oleroma/Grip/media/dev/2.jpg

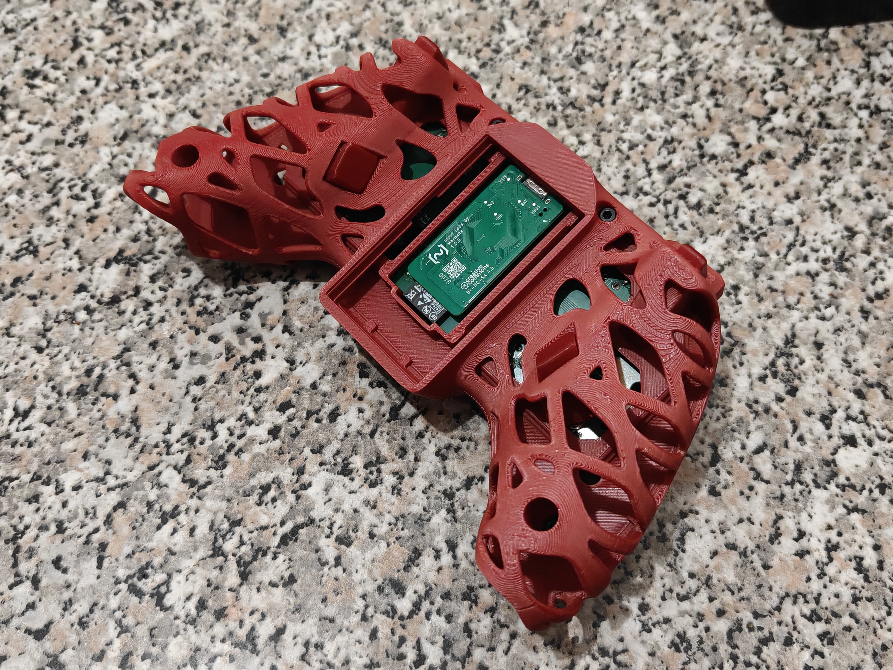
media/dev/2.jpg
