oleroma/Grip/media/dev/3.jpg

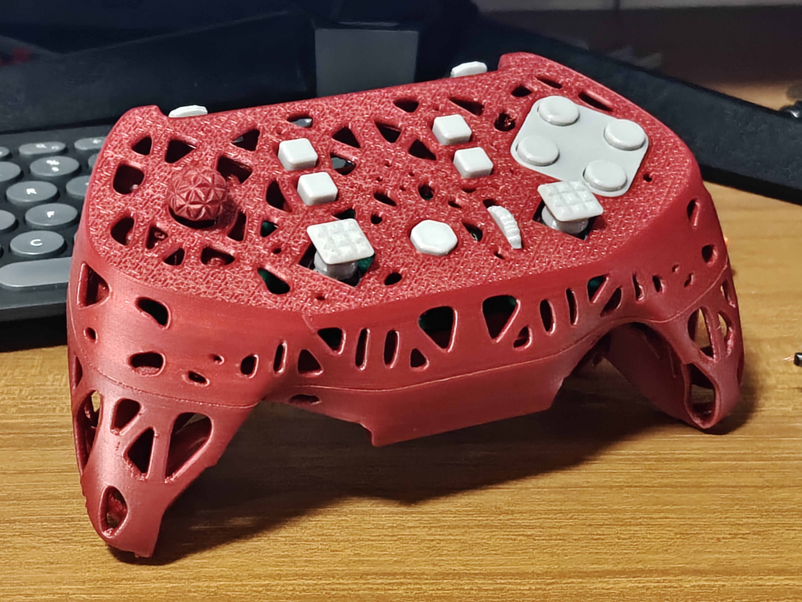
media/dev/3.jpg
