oleroma/Grip/media/dev/4.jpg

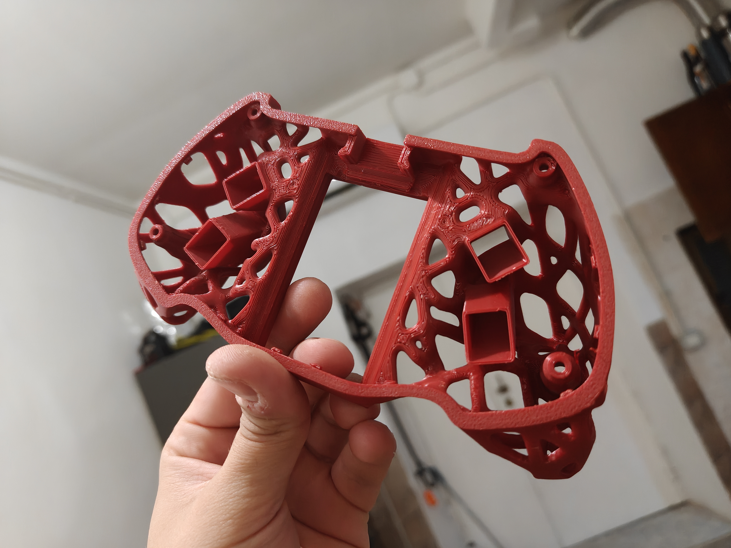
media/dev/4.jpg
