oleroma/Grip/media/dev/GripV_detail.jpg

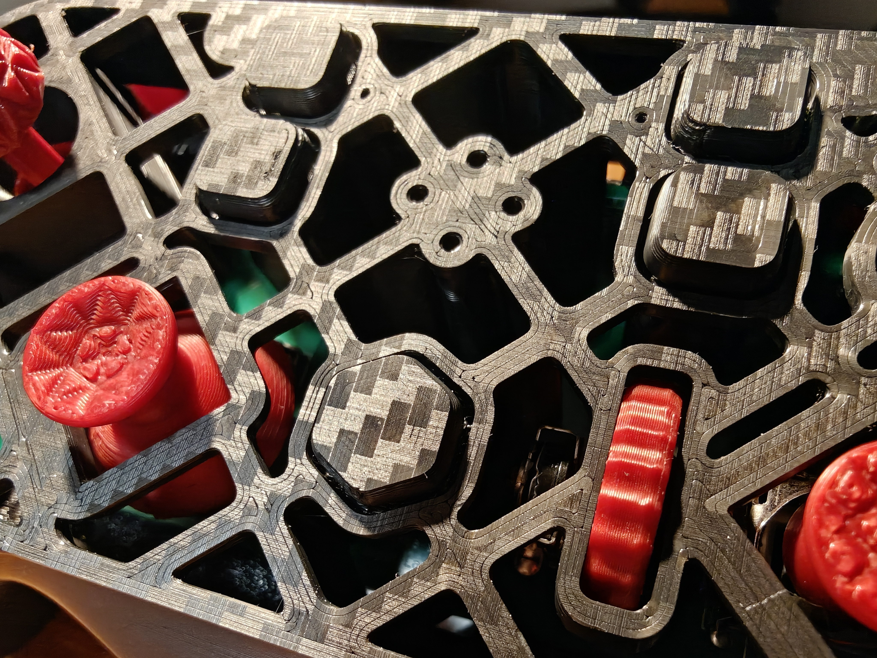
media/dev/GripV_detail.jpg
