oleroma/Grip/media/previews/1.png

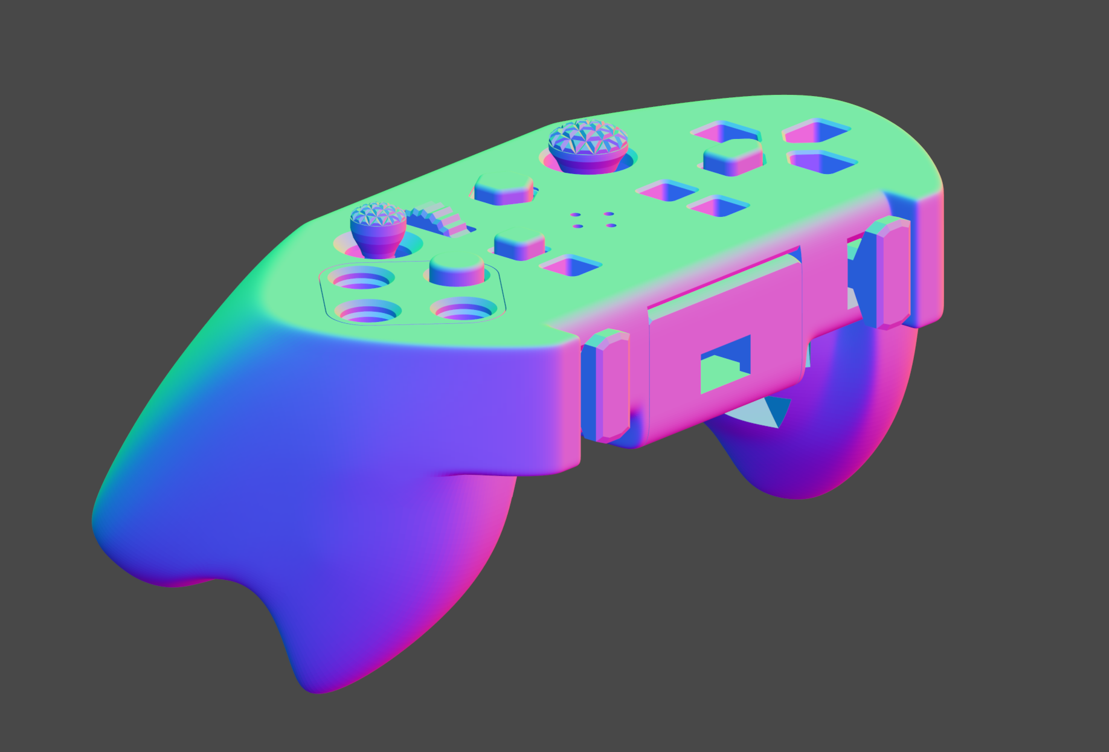
media/previews/1.png
