oleroma/Grip/media/previews/2.png

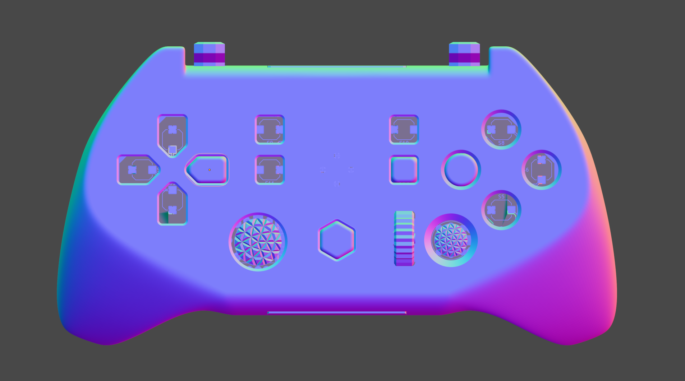
media/previews/2.png
