oleroma/Grip/media/previews/3.png

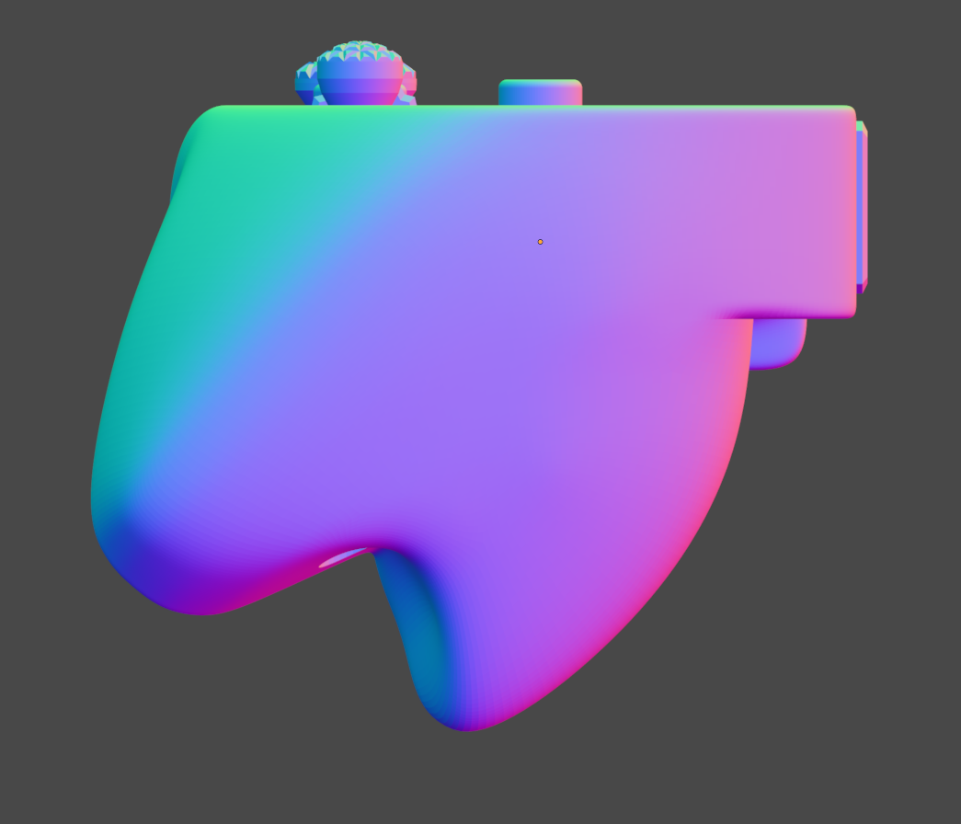
media/previews/3.png
