oleroma/Grip/media/previews/4.png

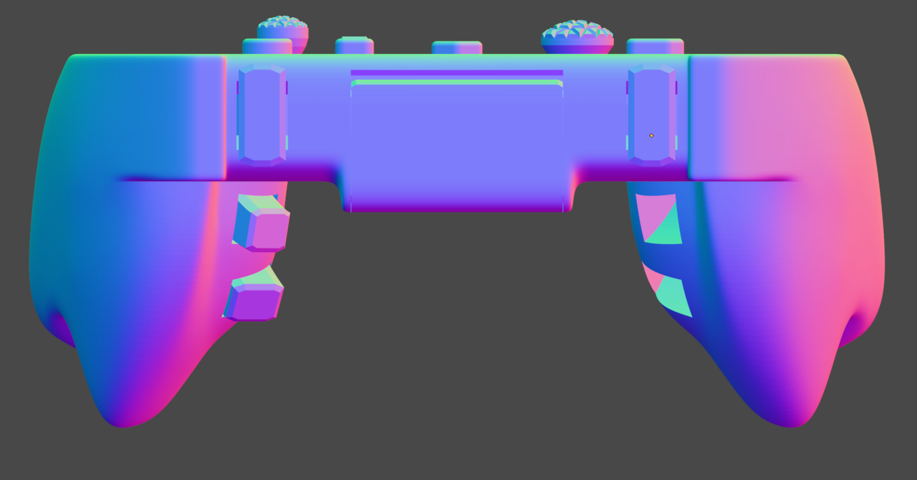
media/previews/4.png
