oleroma/Grip/media/previews/5.png

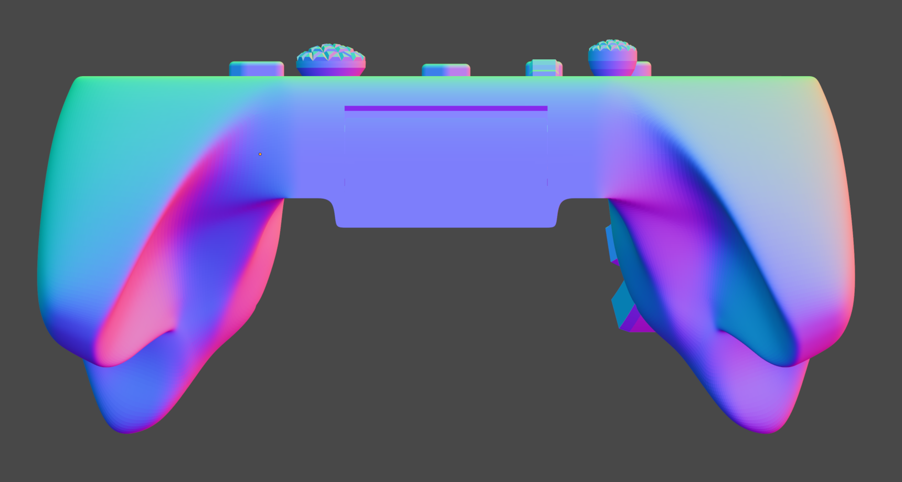
media/previews/5.png
