oleroma/Grip/media/previews/6.png

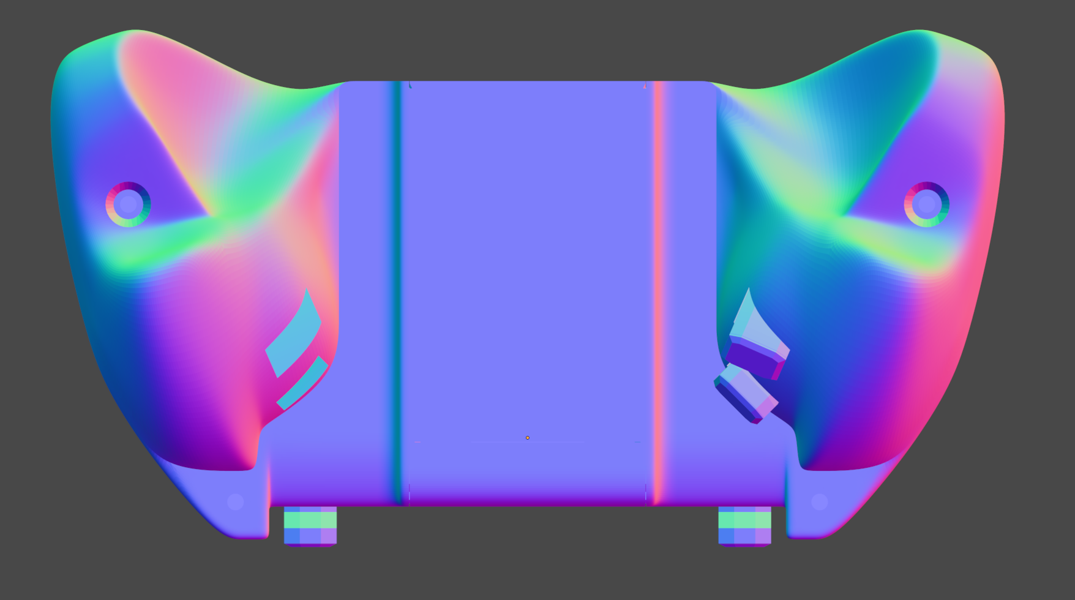
media/previews/6.png
