oleroma/Grip/orca_slicer/GripV/parts/buttons/loose/select_button.stl

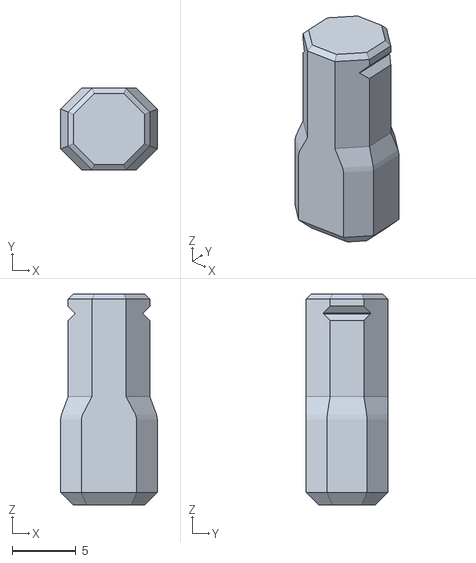
[picture p30: CAD file, 2026-09-15]
orca_slicer/GripV/parts/buttons/loose/select_button.stl
7.60 x 6.40 x 16.6
