oleroma/Grip/orca_slicer/GripV/parts/dpad_stick/dpad_stick_cap.stl

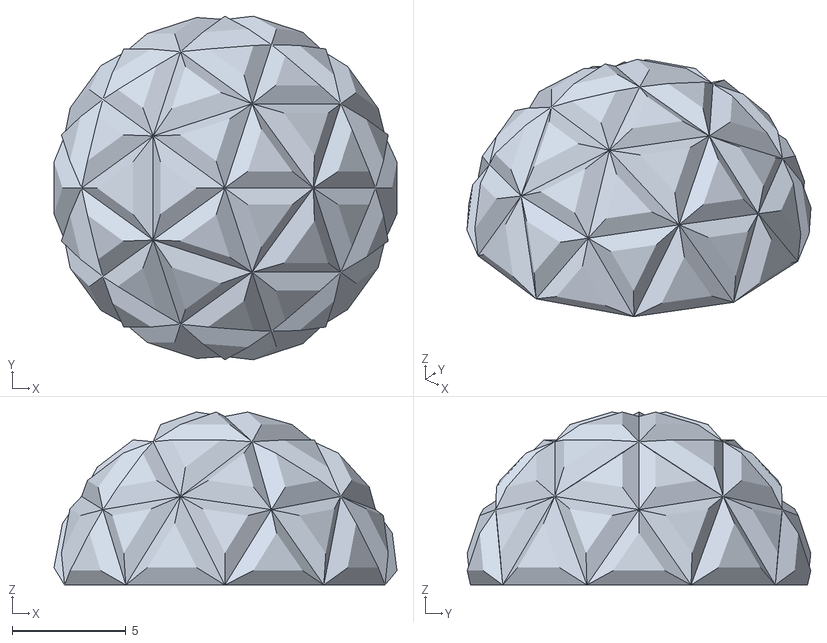
[picture p31: CAD file, 2026-09-17]
orca_slicer/GripV/parts/dpad_stick/dpad_stick_cap.stl
15.1 x 15.1 x 7.60
