oleroma/Grip/orca_slicer/GripV/parts/scrollwheel/scrollwheel_holder.stl

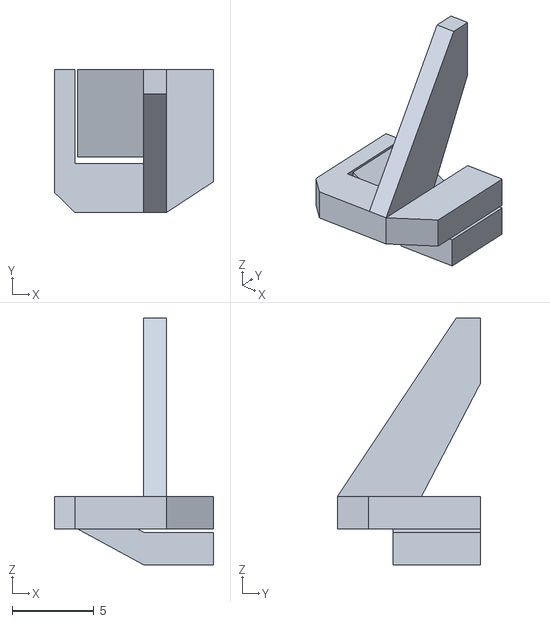
[picture p32: CAD file, 2026-09-15]
orca_slicer/GripV/parts/scrollwheel/scrollwheel_holder.stl
9.77 x 8.79 x 15.2
