oleroma/Grip/orca_slicer/GripV/parts/StickR.stl

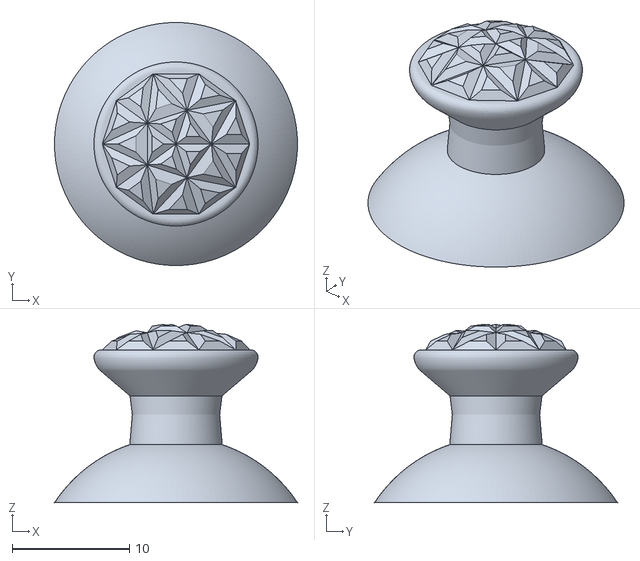
[picture p33: CAD file, 2026-09-20]
orca_slicer/GripV/parts/StickR.stl
20.7 x 20.7 x 15.2
