oleroma/Grip/orca_slicer/GripV/parts/sticks/circle_top/concave/10_deg/StickL.stl

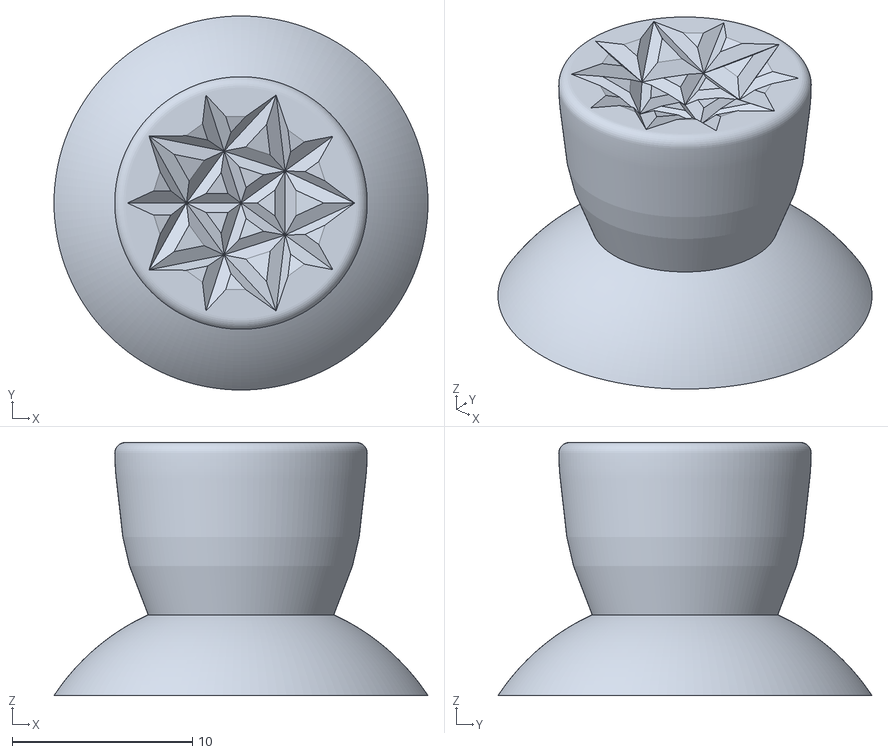
[picture p34: CAD file, 2026-09-20]
orca_slicer/GripV/parts/sticks/circle_top/concave/10_deg/StickL.stl
20.7 x 20.7 x 14.0
