oleroma/Grip/orca_slicer/GripV/parts/sticks/circle_top/convex/10_deg/StickL.stl

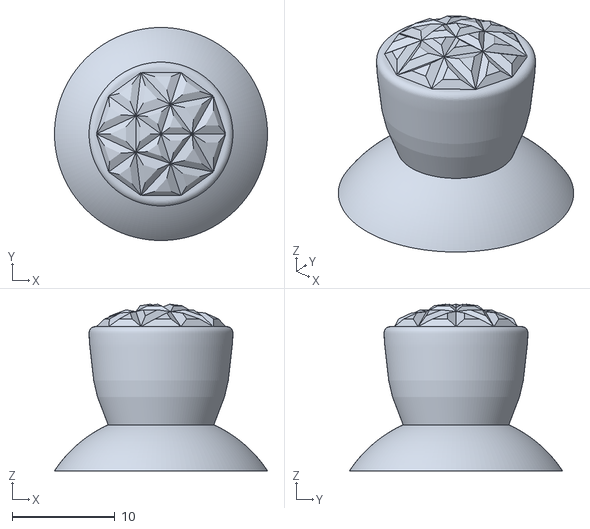
[picture p35: CAD file, 2026-09-20]
orca_slicer/GripV/parts/sticks/circle_top/convex/10_deg/StickL.stl
20.7 x 20.7 x 16.2
