oleroma/Grip/orca_slicer/GripV/parts/sticks/square_top/concave/10_deg/StickR.stl

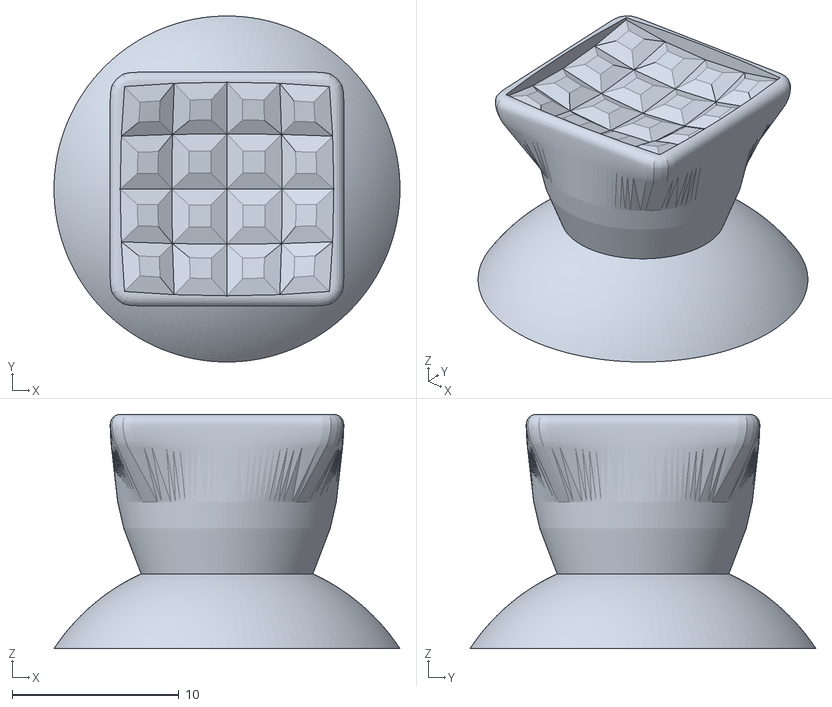
[picture p36: CAD file, 2026-09-20]
orca_slicer/GripV/parts/sticks/square_top/concave/10_deg/StickR.stl
20.7 x 20.7 x 14.0
