oleroma/Grip/orca_slicer/GripV/parts/sticks/square_top/convex/12_deg/StickR.stl

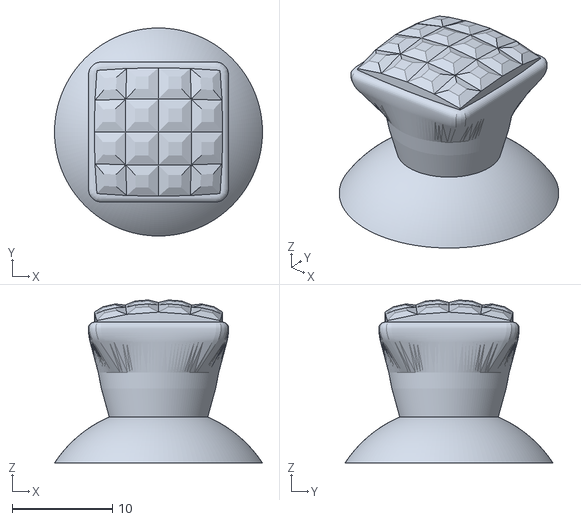
[picture p38: CAD file, 2026-09-20]
orca_slicer/GripV/parts/sticks/square_top/convex/12_deg/StickR.stl
20.7 x 20.7 x 16.2
