oleroma/Grip/orca_slicer/GripV/parts/triggers/default/press_default/R2.stl

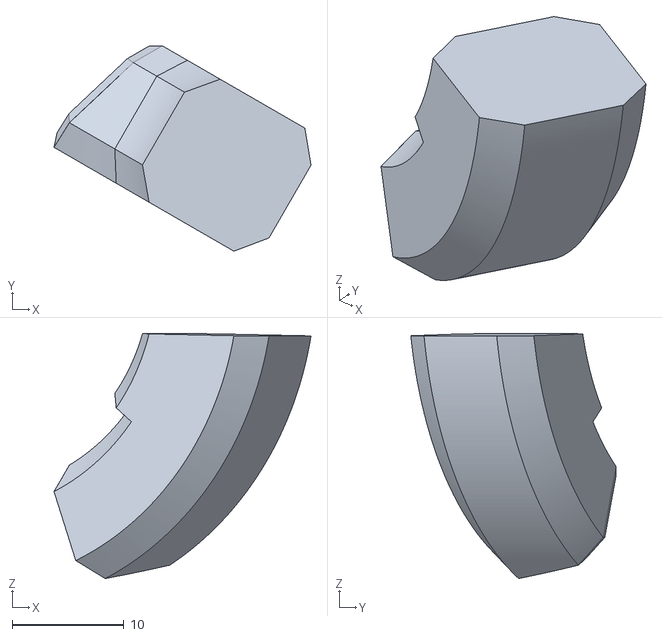
[picture p39: CAD file, 2026-09-15]
orca_slicer/GripV/parts/triggers/default/press_default/R2.stl
23.0 x 18.4 x 21.9
