oleroma/Grip/orca_slicer/GripV/parts/triggers/default/press_tight/L4.stl

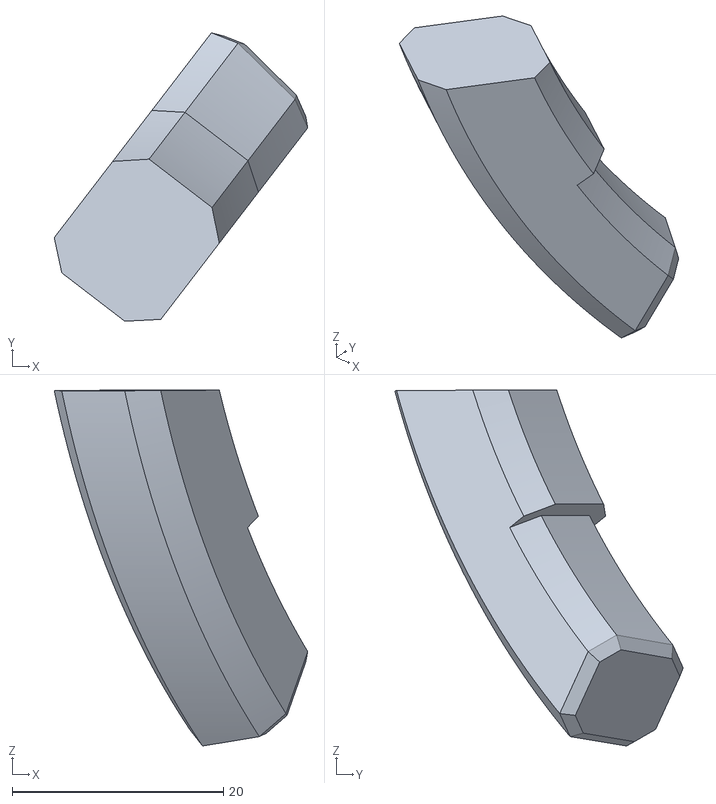
[picture p40: CAD file, 2026-09-15]
orca_slicer/GripV/parts/triggers/default/press_tight/L4.stl
24.0 x 27.3 x 33.7
