oleroma/Grip/orca_slicer/GripV/parts/triggers/loose/press_default/L4.stl

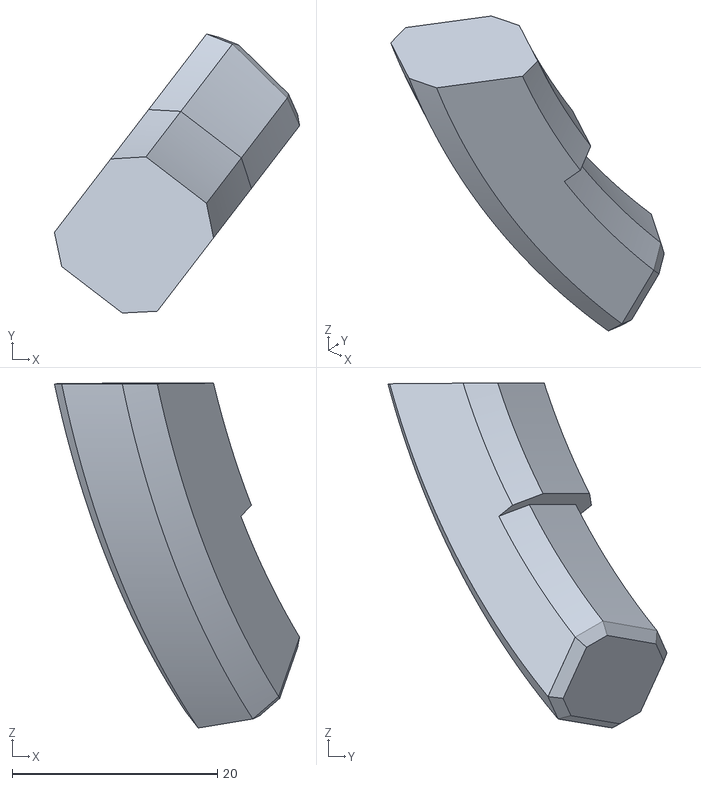
[picture p41: CAD file, 2026-09-15]
orca_slicer/GripV/parts/triggers/loose/press_default/L4.stl
23.9 x 27.2 x 33.6
