oleroma/Grip/orca_slicer/GripV/za3tarani/case_middle_plate.stl

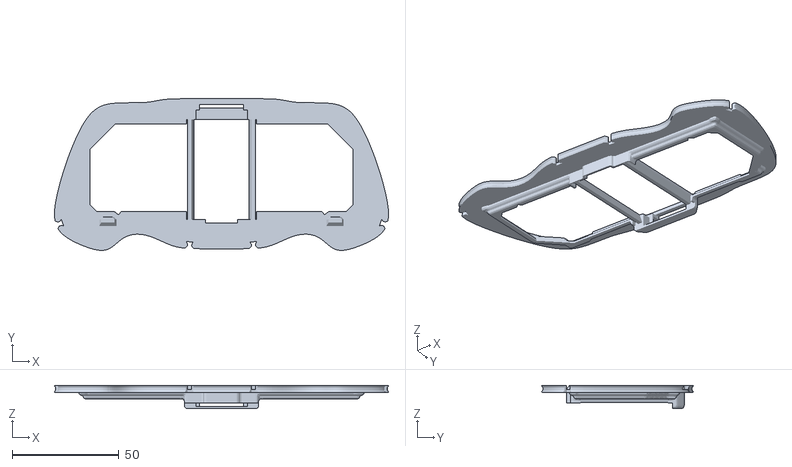
[picture p43: CAD file, 2026-09-20]
orca_slicer/GripV/za3tarani/case_middle_plate.stl
156.3 x 71.0 x 10.8
