oleroma/Grip/orca_slicer/GripX/DS_style/bumpers/L1_pr_loose.stl

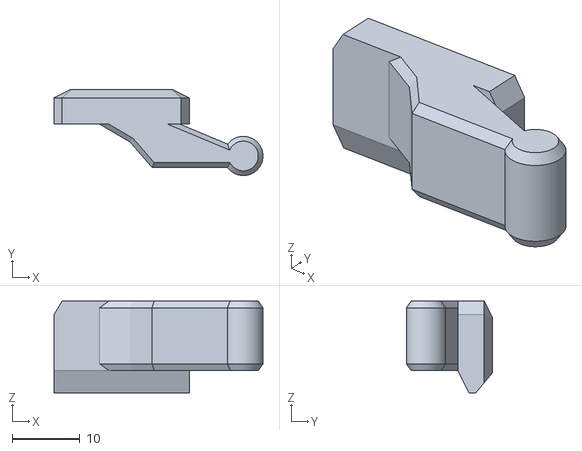
[picture p44: CAD file, 2026-09-15]
orca_slicer/GripX/DS_style/bumpers/L1_pr_loose.stl
30.9 x 12.7 x 13.6
