oleroma/Grip/orca_slicer/GripX/DS_style/bumpers/press_default/L1.stl

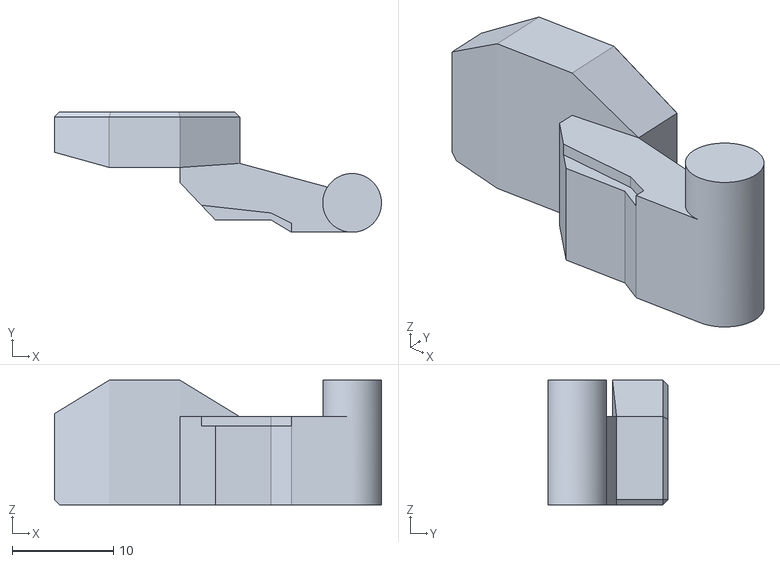
[picture p45: CAD file, 2026-09-20]
orca_slicer/GripX/DS_style/bumpers/press_default/L1.stl
32.3 x 11.9 x 12.3
