oleroma/Grip/orca_slicer/GripX/DS_style/case_standard/case_top_cap_knob_dpad_stick.stl

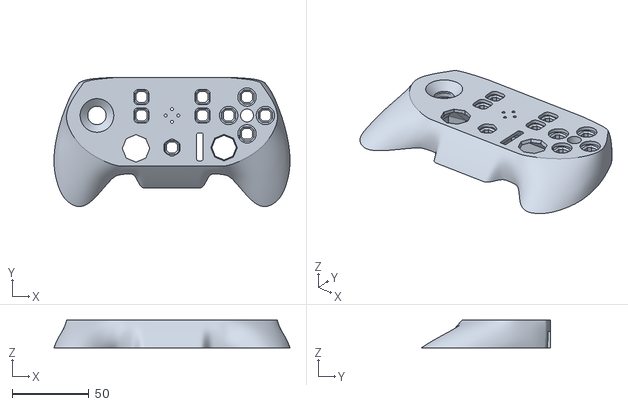
[picture p46: CAD file, 2026-09-20]
orca_slicer/GripX/DS_style/case_standard/case_top_cap_knob_dpad_stick.stl
154.1 x 84.3 x 18.0
