oleroma/Grip/orca_slicer/GripX/DS_style/triggers/default/press_default/R2.stl

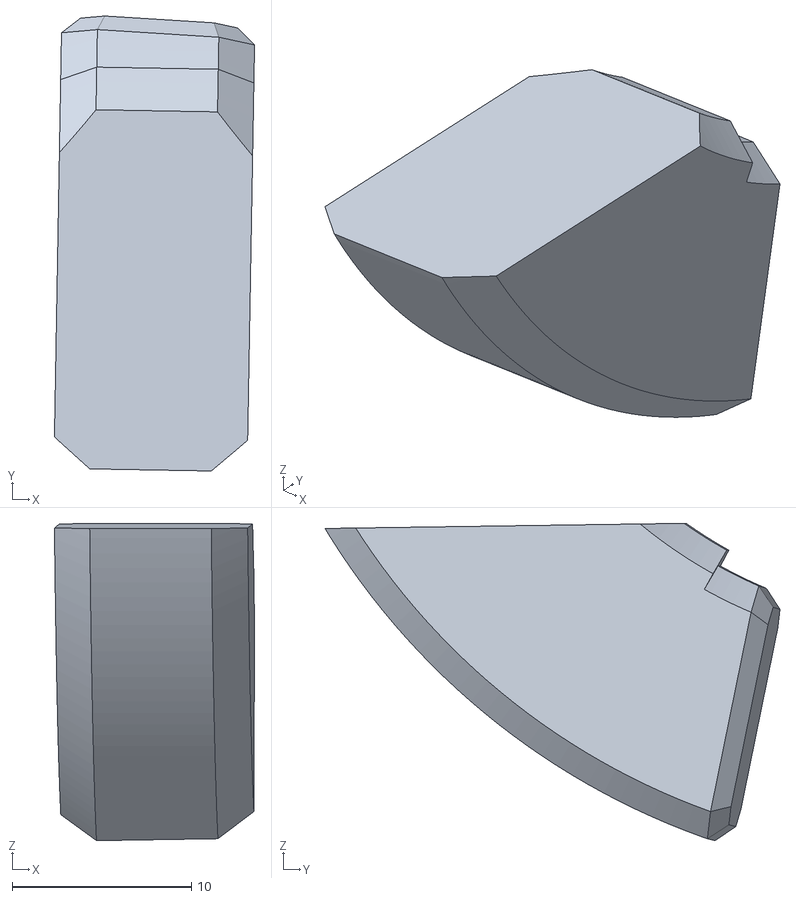
[picture p47: CAD file, 2026-09-15]
orca_slicer/GripX/DS_style/triggers/default/press_default/R2.stl
11.2 x 25.4 x 17.7
