oleroma/Grip/orca_slicer/GripX/DS_style/triggers/loose/press_loose/L4.stl

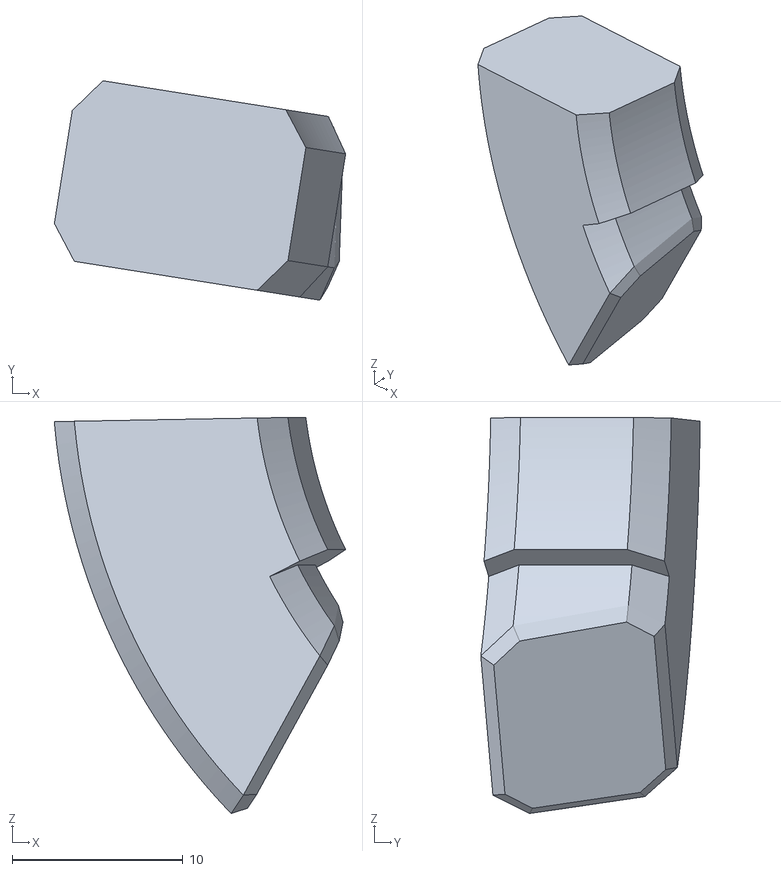
[picture p48: CAD file, 2026-09-15]
orca_slicer/GripX/DS_style/triggers/loose/press_loose/L4.stl
17.0 x 12.8 x 23.2
