oleroma/Grip/orca_slicer/GripX/parts/buttons/default/abxy_button.stl

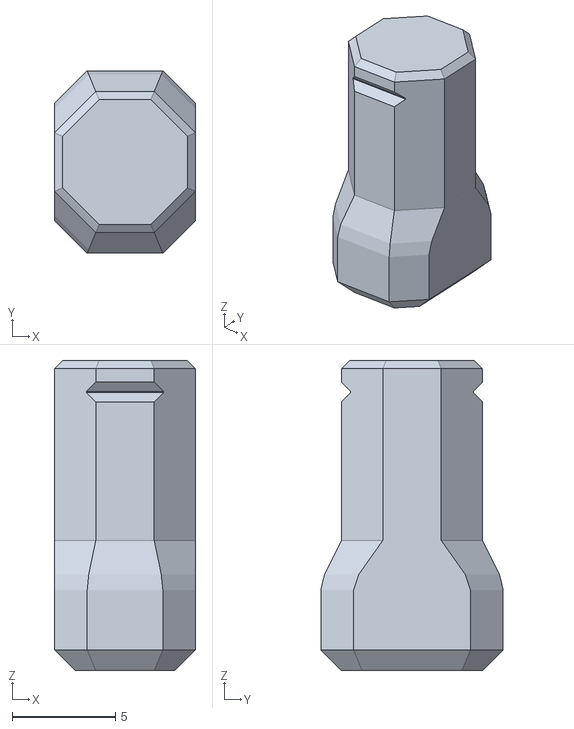
[picture p49: CAD file, 2026-09-15]
orca_slicer/GripX/parts/buttons/default/abxy_button.stl
6.84 x 8.84 x 15.0
