oleroma/Grip/orca_slicer/GripX/parts/buttons/default/caps_default/abxy_cap_down.stl

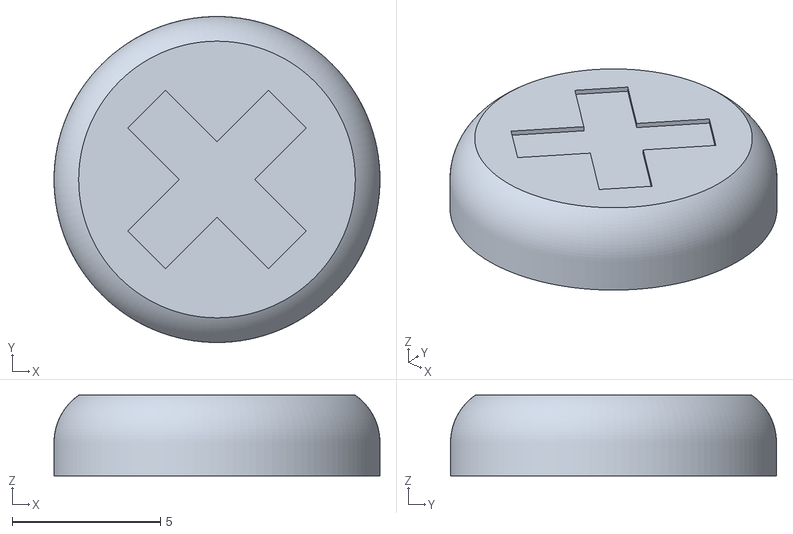
[picture p50: CAD file, 2026-09-20]
orca_slicer/GripX/parts/buttons/default/caps_default/abxy_cap_down.stl
11.0 x 11.0 x 2.72
