oleroma/Grip/orca_slicer/GripX/parts/buttons/loose/home_button.stl

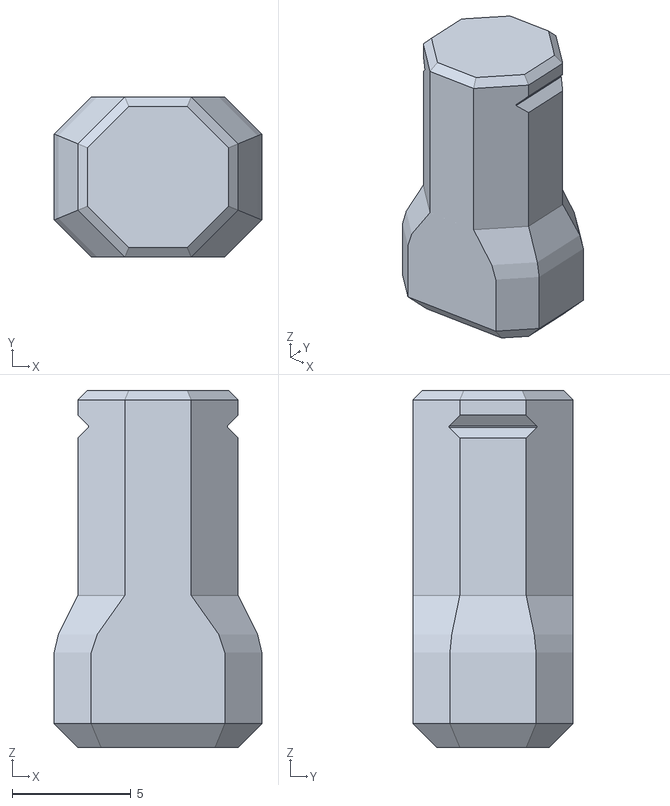
[picture p51: CAD file, 2026-09-15]
orca_slicer/GripX/parts/buttons/loose/home_button.stl
8.74 x 6.74 x 15.0
