oleroma/Grip/orca_slicer/GripX/parts/buttons/tight/dpad_button.stl

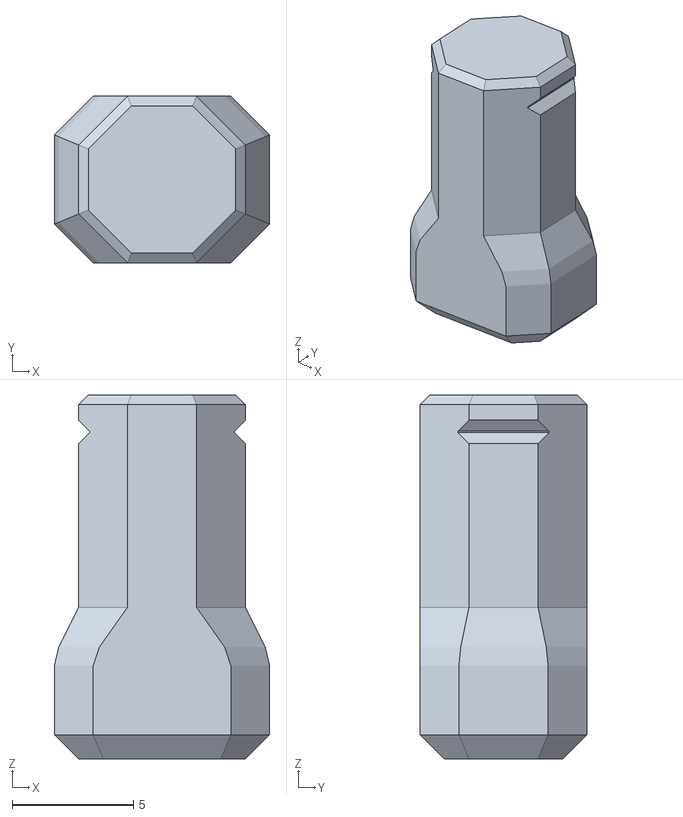
[picture p52: CAD file, 2026-09-15]
orca_slicer/GripX/parts/buttons/tight/dpad_button.stl
8.88 x 6.88 x 15.0
