oleroma/Grip/orca_slicer/GripX/parts/dpad_stick/rocker_support.stl

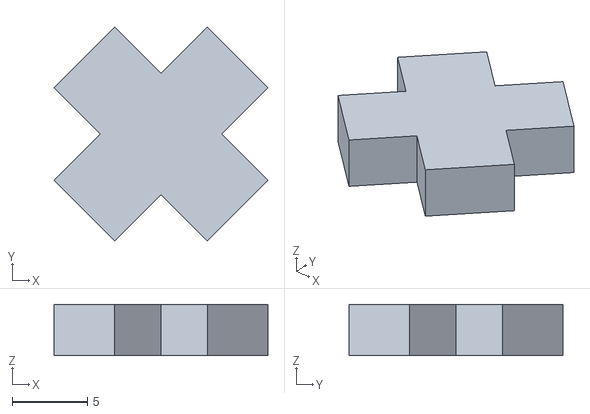
[picture p53: CAD file, 2026-09-15]
orca_slicer/GripX/parts/dpad_stick/rocker_support.stl
14.2 x 14.2 x 3.40
