oleroma/Grip/orca_slicer/GripX/parts/scrollwheel/scrollwheel_core.stl

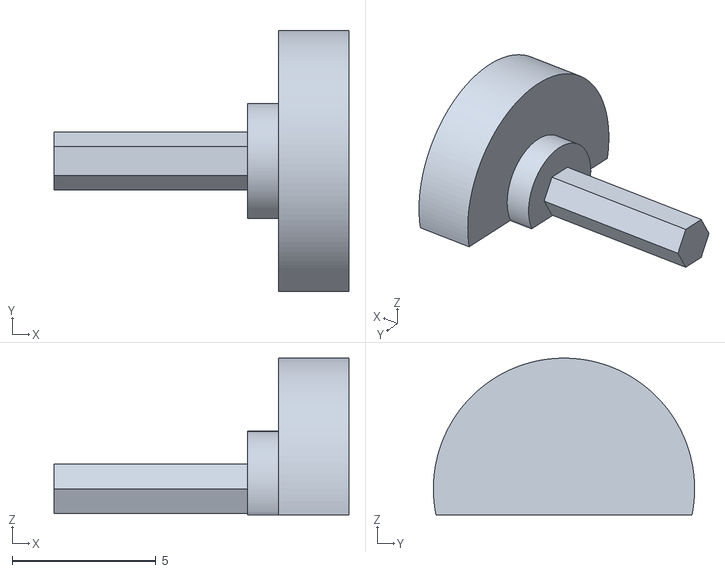
[picture p54: CAD file, 2026-09-15]
orca_slicer/GripX/parts/scrollwheel/scrollwheel_core.stl
10.2 x 9.08 x 5.44
