oleroma/Grip/orca_slicer/GripX/parts/StickL.stl

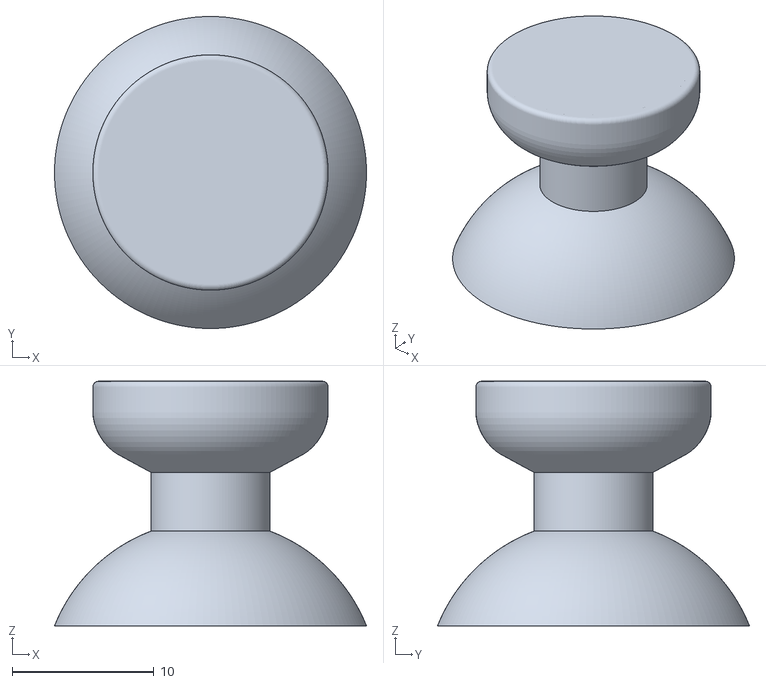
[picture p55: CAD file, 2026-09-20]
orca_slicer/GripX/parts/StickL.stl
22.0 x 22.0 x 17.3
