oleroma/Grip/orca_slicer/GripX/Xbox_style/bumpers/press_loose/L1.stl

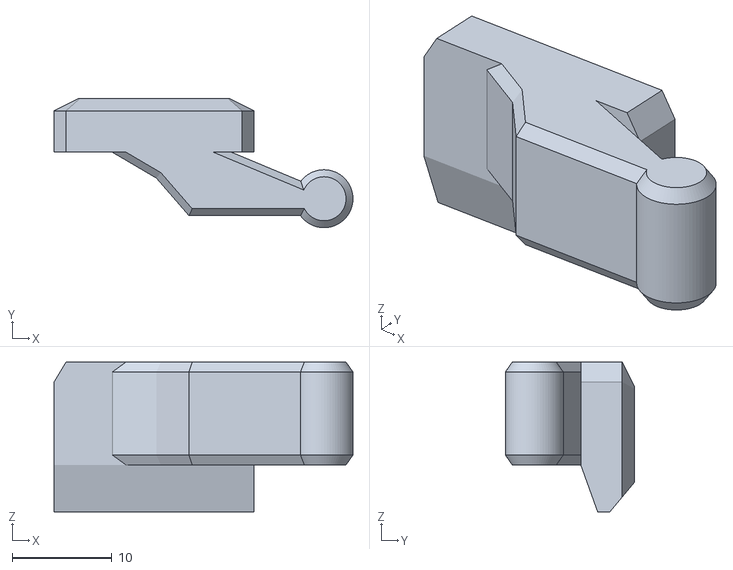
[picture p56: CAD file, 2026-09-15]
orca_slicer/GripX/Xbox_style/bumpers/press_loose/L1.stl
29.9 x 12.9 x 15.0
