oleroma/Grip/orca_slicer/GripX/Xbox_style/case_standard/case_top_cap_knob_dpad_stick.stl

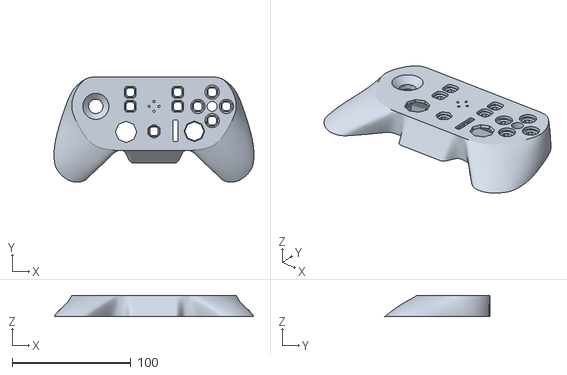
[picture p57: CAD file, 2026-09-20]
orca_slicer/GripX/Xbox_style/case_standard/case_top_cap_knob_dpad_stick.stl
168.5 x 88.6 x 18.0
