oleroma/Grip/orca_slicer/GripX/Xbox_style/triggers/loose/press_loose/L4.stl

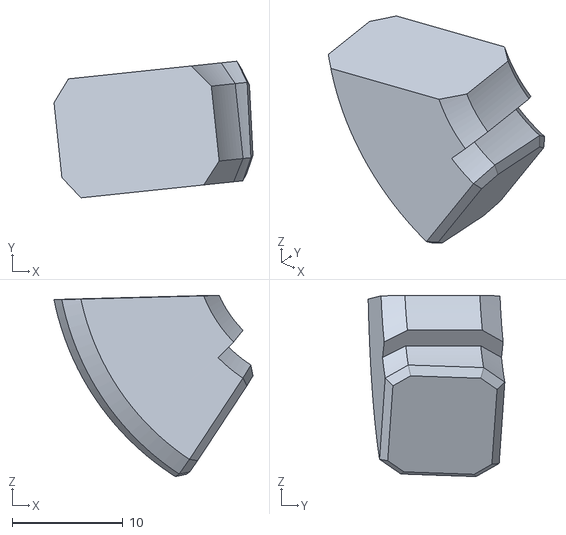
[picture p58: CAD file, 2026-09-15]
orca_slicer/GripX/Xbox_style/triggers/loose/press_loose/L4.stl
18.0 x 12.3 x 16.4
