oleroma/Grip/orca_slicer/GripV/GripV_case_hollow.3mf

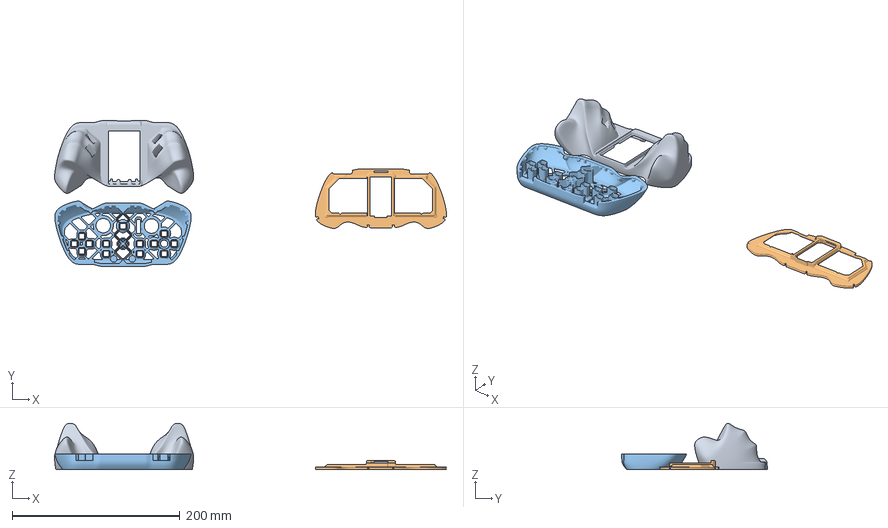
[picture p59: CAD file, 2026-09-20]
orca_slicer/GripV/GripV_case_hollow.3mf
467.0 x 173.3 x 55.4 mm
case_bottom.stl
case_middle_plate.stl
case_top
