oleroma/Grip/orca_slicer/GripV/parts/buttons/default/caps_loose/select_cap_top_right.stl

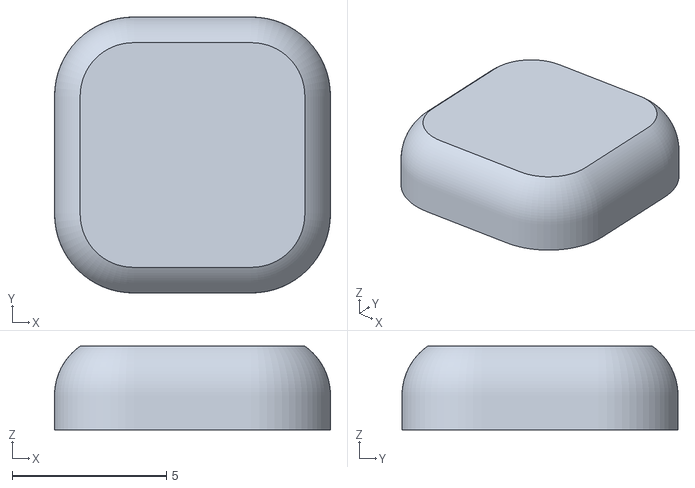
[picture p60: CAD file, 2026-09-15]
orca_slicer/GripV/parts/buttons/default/caps_loose/select_cap_top_right.stl
8.96 x 8.96 x 2.72
