oleroma/Grip/orca_slicer/GripV/parts/buttons/loose/caps_default/home_cap.stl

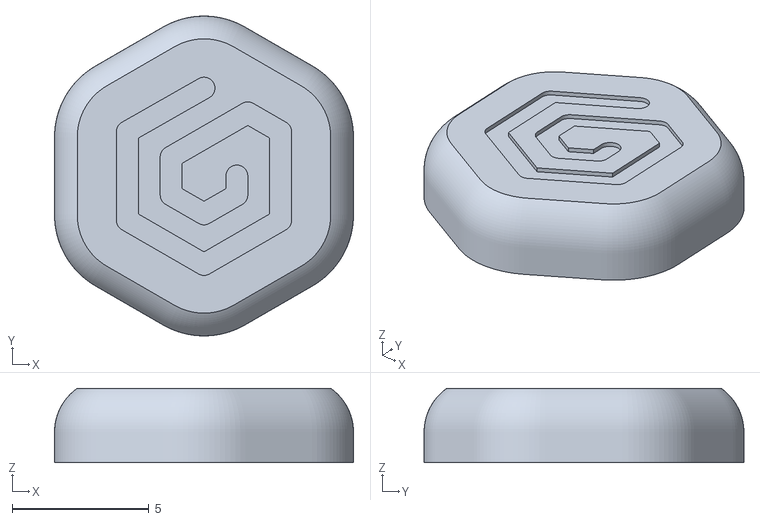
[picture p61: CAD file, 2026-09-15]
orca_slicer/GripV/parts/buttons/loose/caps_default/home_cap.stl
10.9 x 11.7 x 2.72
