oleroma/Grip/orca_slicer/GripV/parts/buttons/loose/caps_tight/dpad_cap_down.stl

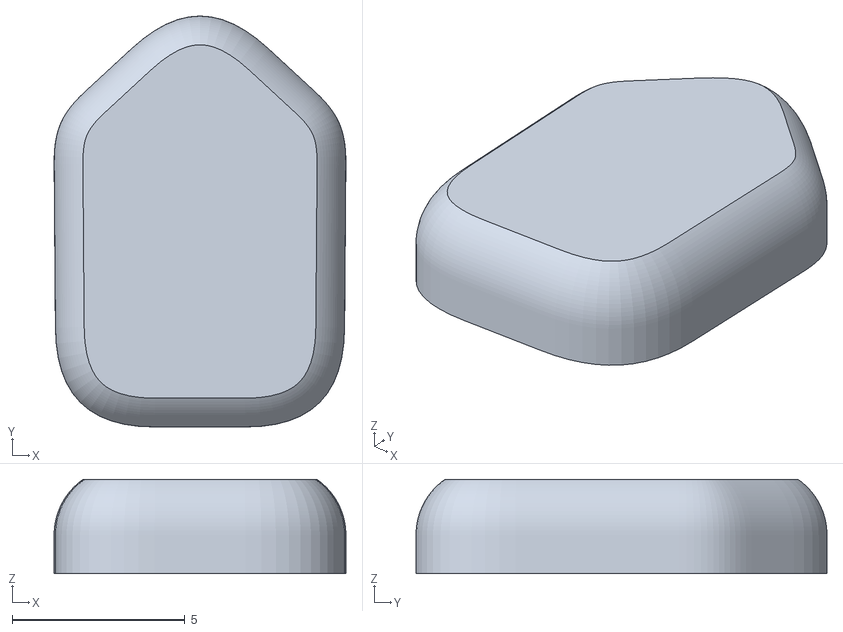
[picture p62: CAD file, 2026-09-15]
orca_slicer/GripV/parts/buttons/loose/caps_tight/dpad_cap_down.stl
8.44 x 11.9 x 2.72
