oleroma/Grip/orca_slicer/GripV/parts/buttons/tight/caps_default/dpad_cap_right.stl

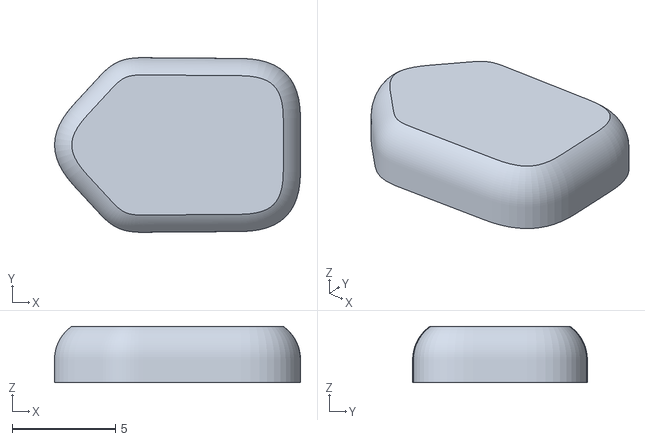
[picture p63: CAD file, 2026-09-15]
orca_slicer/GripV/parts/buttons/tight/caps_default/dpad_cap_right.stl
11.9 x 8.44 x 2.72
